Electro707/p1010_camera_remote_shutter_v2/Firmware/F1012_Main/stateScreensaver.h

/**
 * Screensaver module
 * jb, 2025
 *
 * this module handles drawing a rotating 3d camera as a screensaver
 *
 * screen"saver", I think this is more compute than the main app as a whole
 */
#ifndef SCREENSAVER_H
#define SCREENSAVER_H

void serviceScreenSaverState(void);

#endif
