Electro707/p1010_camera_remote_shutter_v2/Firmware/F1012_Main/bitmap.c

#include "bitmap.h"

const uint8_t batteryBase[55] = {
        0xff,0xff,0xff,0x8f,
        0xff,0xff,0xff,0xc7,
        0x00,0x00,0x00,0x63,
        0x00,0x00,0x80,0x33,
        0x00,0x00,0xc0,0x1b,
        0x00,0x00,0xe0,0x0f,
        0x00,0x00,0xf0,0x07,
        0x00,0x00,0xf8,0x03,
        0x00,0x00,0xfc,0x01,
        0x00,0x00,0xde,0x00,
        0x00,0x00,0x67,0x00,
        0x00,0x80,0xf1,0xff,
        0xff,0xff,0xf8,0xff,
        0xff,0x7f,0x00};

const uint8_t batteryCharge[55] = {
        0xff,0xff,0xff,0x8f,
        0xff,0xff,0xff,0xc7,
        0x00,0x00,0x00,0x63,
        0x00,0x04,0x8c,0x33,
        0x80,0x03,0xc3,0x1b,
        0xe0,0xc3,0xe0,0x0f,
        0xb8,0x31,0xf0,0x07,
        0xc6,0x0e,0xf8,0x83,
        0xe1,0x03,0xfc,0x61,
        0xe0,0x00,0xde,0x18,
        0x10,0x00,0x67,0x00,
        0x00,0x80,0xf1,0xff,
        0xff,0xff,0xf8,0xff,
        0xff,0x7f,0x00};
