Electro707/p1010_camera_remote_shutter_v2/Firmware/F1012_Main/bitmap.h

#ifndef BITMAP_H
#define BITMAP_H

#include <stdint.h>

#define IMG_W_batteryBase 31
#define IMG_H_batteryBase 14
extern const uint8_t batteryBase[55];

#define IMG_W_batteryCharge 31
#define IMG_H_batteryCharge 14
extern const uint8_t batteryCharge[55];

#endif
