Electro707/p1010_camera_remote_shutter_v2/Firmware/test_lcd_camRender3/objCamera.h

/* defines for object */
#define VERTEX_SIZE 32
#define EDGE_SIZE 48
#define FACE_SIZE 52
#define NORMAL_SIZE 22
#define OBJ_TYPES_N 3
float objectVertex[VERTEX_SIZE*4] = {
	2.000000, 1.000000, -0.750000, 1.000000,
	2.000000, -1.000000, -0.750000, 1.000000,
	2.000000, 1.000000, 0.750000, 1.000000,
	2.000000, -1.000000, 0.750000, 1.000000,
	-2.000000, 1.000000, -0.750000, 1.000000,
	-2.000000, -1.000000, -0.750000, 1.000000,
	-2.000000, 1.000000, 0.750000, 1.000000,
	-2.000000, -1.000000, 0.750000, 1.000000,
	0.000000, 0.750000, -1.500000, 1.000000,
	0.000000, 0.750000, -0.750000, 1.000000,
	0.530330, 0.530330, -1.500000, 1.000000,
	0.530330, 0.530330, -0.750000, 1.000000,
	0.750000, 0.000000, -1.500000, 1.000000,
	0.750000, -0.000000, -0.750000, 1.000000,
	0.530330, -0.530330, -1.500000, 1.000000,
	0.530330, -0.530330, -0.750000, 1.000000,
	0.000000, -0.750000, -1.500000, 1.000000,
	0.000000, -0.750000, -0.750000, 1.000000,
	-0.530330, -0.530330, -1.500000, 1.000000,
	-0.530330, -0.530330, -0.750000, 1.000000,
	-0.750000, 0.000000, -1.500000, 1.000000,
	-0.750000, -0.000000, -0.750000, 1.000000,
	-0.530330, 0.530330, -1.500000, 1.000000,
	-0.530330, 0.530330, -0.750000, 1.000000,
	-1.600000, 1.000000, 0.300000, 1.000000,
	-1.600000, 1.300000, 0.300000, 1.000000,
	-1.600000, 1.000000, -0.300000, 1.000000,
	-1.600000, 1.300000, -0.300000, 1.000000,
	-1.000000, 1.000000, 0.300000, 1.000000,
	-1.000000, 1.300000, 0.300000, 1.000000,
	-1.000000, 1.000000, -0.300000, 1.000000,
	-1.000000, 1.300000, -0.300000, 1.000000,
};
uint objectEdge[EDGE_SIZE*2] =     {
	2, 0,	0, 4,	7, 3,	3, 2,
	5, 7,	7, 6,	5, 1,	3, 1,
	1, 0,	5, 4,	4, 6,	6, 2,
	10, 8,	8, 9,	12, 10,	10, 11,
	14, 12,	12, 13,	16, 14,	14, 15,
	18, 16,	16, 17,	20, 18,	18, 19,
	22, 20,	20, 21,	8, 22,	22, 23,
	9, 11,	11, 13,	13, 15,	15, 17,
	17, 19,	19, 21,	9, 23,	23, 21,
	26, 24,	24, 25,	30, 26,	26, 27,
	28, 30,	30, 31,	24, 28,	28, 29,
	29, 31,	31, 27,	25, 27,	29, 25,
};
uint objectFace[FACE_SIZE*3] =     {
	4, 2, 0,	2, 7, 3,
	6, 5, 7,	1, 7, 5,
	0, 3, 1,	4, 1, 5,
	4, 6, 2,	2, 6, 7,
	6, 4, 5,	1, 3, 7,
	0, 2, 3,	4, 0, 1,
	9, 10, 8,	11, 12, 10,
	13, 14, 12,	15, 16, 14,
	17, 18, 16,	19, 20, 18,
	21, 17, 13,	21, 22, 20,
	23, 8, 22,	14, 18, 22,
	9, 11, 10,	11, 13, 12,
	13, 15, 14,	15, 17, 16,
	17, 19, 18,	19, 21, 20,
	13, 11, 9,	9, 23, 21,
	21, 19, 17,	17, 15, 13,
	13, 9, 21,	21, 23, 22,
	23, 9, 8,	22, 8, 10,
	10, 12, 14,	14, 16, 18,
	18, 20, 22,	22, 10, 14,
	25, 26, 24,	27, 30, 26,
	31, 28, 30,	29, 24, 28,
	30, 24, 26,	27, 29, 31,
	25, 27, 26,	27, 31, 30,
	31, 29, 28,	29, 25, 24,
	30, 28, 24,	27, 25, 29,
};
float objectNormal[NORMAL_SIZE*4] =     {
	-0.000000, 1.000000, -0.000000, 1.000000,
	-0.000000, -0.000000, 1.000000, 1.000000,
	-1.000000, -0.000000, -0.000000, 1.000000,
	-0.000000, -1.000000, -0.000000, 1.000000,
	1.000000, -0.000000, -0.000000, 1.000000,
	-0.000000, -0.000000, -1.000000, 1.000000,
	0.382700, 0.923900, -0.000000, 1.000000,
	0.923900, 0.382700, -0.000000, 1.000000,
	0.923900, -0.382700, -0.000000, 1.000000,
	0.382700, -0.923900, -0.000000, 1.000000,
	-0.382700, -0.923900, -0.000000, 1.000000,
	-0.923900, -0.382700, -0.000000, 1.000000,
	-0.000000, -0.000000, 1.000000, 1.000000,
	-0.923900, 0.382700, -0.000000, 1.000000,
	-0.382700, 0.923900, -0.000000, 1.000000,
	-0.000000, -0.000000, -1.000000, 1.000000,
	-1.000000, -0.000000, -0.000000, 1.000000,
	-0.000000, -0.000000, -1.000000, 1.000000,
	1.000000, -0.000000, -0.000000, 1.000000,
	-0.000000, -0.000000, 1.000000, 1.000000,
	-0.000000, -1.000000, -0.000000, 1.000000,
	-0.000000, 1.000000, -0.000000, 1.000000,
};
uint objectNormalFaceIdx[FACE_SIZE] =     {
0, 1, 2, 3, 4, 5, 0, 1, 2, 3, 4, 5, 6, 7, 8, 9, 10, 11, 12, 13, 14, 15, 6, 7, 8, 9, 10, 11, 12, 12, 12, 12, 12, 13, 14, 15, 15, 15, 15, 15, 16, 17, 18, 19, 20, 21, 16, 17, 18, 19, 20, 21, };
uint objectTypeSplitFace[OBJ_TYPES_N] =     {
12, 40, 52, };
